DanushkaDissanayaka/Qbot/arduino-Src/lineFollow.h

#ifndef lineFollow_h
    #define lineFollow_h
    #include "QTRSensor.h"
    #include "motor.h"
    #include "irSensor.h"

    #define LINE_FLLOW_DEBUG    false

    // Full speed PID Values
    double FULL_SPEED_Kp =  0.158;//0.080; 0.340
    double FULL_SPEED_Kd =  20;//0.890; 1.71
    #define FULL_SPEED_Ki   0

    #define BACKWORD_STOP_DELAY     80 // no need
    #define ROTATE_STOP_DELAY       40

    // Half Speed PID values
    #define HALF_SPEED_Kp 0
    #define HALF_SPEED_Kd 0
    #define HALF_SPEED_Ki 0

    #define LINE_POSITION   3500
    #define MIN_VALUE       200
    #define MAX_VALUE       600

    //turning speed values
    #define TURN_SPEED      120
    #define TUNING_SPEED    100

    int             error       = 0;
    int             I           = 0;
    int             lastError   = 0;
    int             motorSpeed  = 0;
    unsigned int    position    = 0;
    bool junctionDetect = false;

    void calPid (float Kp , float Kd , float Ki){
        position = qtra.readLine(sensorValues);
        error =  position - LINE_POSITION;
        I = I + error;
        motorSpeed = (Kp * error) + (Kd * (error - lastError)) + I*Ki;
        lastError = error;
    }

    void fullSpeedLineFollowBlackStrip(void){
        forward(); // make both motors rotate forward
        clear_ISR_Verialble(); // before start line follow clear ISR variables
        while(1){

            calPid(FULL_SPEED_Kp,FULL_SPEED_Kd,FULL_SPEED_Ki); // calculate pid For left and right motors

            if(sensorValues[0] < MIN_VALUE &&sensorValues[1] < MIN_VALUE && sensorValues[2] < MIN_VALUE && sensorValues[3] < MIN_VALUE && sensorValues[4] < MIN_VALUE && sensorValues[5] < MIN_VALUE && sensorValues[6] < MIN_VALUE && sensorValues[7] < MIN_VALUE){
                // lost our line or this canbe dedend
                //backToLine();
                break;
            }
            /*if(sensorValues[0] > MAX_VALUE &&sensorValues[1] > MAX_VALUE && sensorValues[2] > MAX_VALUE && sensorValues[3] > MAX_VALUE && sensorValues[4] > MAX_VALUE && sensorValues[5] > MAX_VALUE && sensorValues[6] > MAX_VALUE && sensorValues[7] > MAX_VALUE){
                break; // found our solution
            }*/
            if (leftDetect || rightDetect){
                junctionDetect = true;
                break; // found a junction
            }
            rightMotorSpeed = FULL_BASE_SPEED_RIGHT - motorSpeed;
            leftMotorSpeed =  FULL_BASE_SPEED_LEFT  + motorSpeed;

            if (rightMotorSpeed > FULL_MOTOR_SPEED_RIGHT )  rightMotorSpeed = FULL_MOTOR_SPEED_RIGHT; // prevent the motor from going beyond max speed
            if (leftMotorSpeed >  FULL_MOTOR_SPEED_LEFT )   leftMotorSpeed  = FULL_MOTOR_SPEED_LEFT; // prevent the motor from going beyond max speed
            if (rightMotorSpeed < 0) rightMotorSpeed = 0; // keep the motor speed positive
            if (leftMotorSpeed < 0) leftMotorSpeed = 0; // keep the motor speed positive   

            if (LINE_FLLOW_DEBUG) {
                Serial.print(position);
                Serial.print("\t");
                Serial.print(error);
                Serial.print("\t");
                Serial.print(leftMotorSpeed);
                Serial.print("\t");
                Serial.print(rightMotorSpeed);
                Serial.print("\t");
                Serial.println();
            }
            else {
                speedControl(leftMotorSpeed,rightMotorSpeed); // change motor speed according PID values
            }
        }
        //ForwordBreak();
    }

    void fullSpeedLineFollowWhiteStrip(void){
        
        while(1){

            calPid(FULL_SPEED_Kp,FULL_SPEED_Kd,FULL_SPEED_Ki); // calculate pid For left and right motors

            if(sensorValues[0] < MIN_VALUE && sensorValues[1] < MIN_VALUE && sensorValues[2] < MIN_VALUE && sensorValues[3] < MIN_VALUE && sensorValues[4] < MIN_VALUE && sensorValues[5] < MIN_VALUE && sensorValues[6] < MIN_VALUE && sensorValues[7] < MIN_VALUE){
                    break; // found our solution
            }

            if(sensorValues[0] > MAX_VALUE && sensorValues[1] > MAX_VALUE && sensorValues[2] > MAX_VALUE && sensorValues[3] > MAX_VALUE && sensorValues[4] > MAX_VALUE && sensorValues[5] > MAX_VALUE && sensorValues[6] > MAX_VALUE && sensorValues[7] > MAX_VALUE){
                // lost our line or this canbe dedend
                //backToLine();
                break;
            }

            rightMotorSpeed = FULL_BASE_SPEED_RIGHT + motorSpeed;
            leftMotorSpeed =  FULL_BASE_SPEED_LEFT  - motorSpeed;

            if (rightMotorSpeed > FULL_MOTOR_SPEED_RIGHT )  rightMotorSpeed = FULL_MOTOR_SPEED_RIGHT; // prevent the motor from going beyond max speed
            if (leftMotorSpeed >  FULL_MOTOR_SPEED_LEFT )   leftMotorSpeed  = FULL_MOTOR_SPEED_LEFT; // prevent the motor from going beyond max speed
            if (rightMotorSpeed < 0) rightMotorSpeed = 0; // keep the motor speed positive
            if (leftMotorSpeed < 0) leftMotorSpeed = 0; // keep the motor speed positive   

            if (LINE_FLLOW_DEBUG) {
                Serial.print(position);
                Serial.print("\t");
                Serial.print(error);
                Serial.print("\t");
                Serial.print(leftMotorSpeed);
                Serial.print("\t");
                Serial.print(rightMotorSpeed);
                Serial.print("\t");
                Serial.println();
            }
            else {
                forward();
                speedControl(leftMotorSpeed,rightMotorSpeed); // change motor speed according PID values
            }
        }
        Stop(); // stop both motors after line Follow
    }

    void backToLine(void){
        speedControl(120,120);
        backward();
        delay(50);
        Stop();
    }

    void BlackTuneLine(void){
        // tune line after turn
    }

    void BlackLinetTurnLeft(void){
        //turn right with line referance
        speedControl(0,0);
        turnRight();

        position = qtra.readLine(sensorValues);

         while(sensorValues[6] < MIN_VALUE){
             position = qtra.readLine(sensorValues);
             speedControl(TURN_SPEED,TURN_SPEED);
         }

            speedControl(0,0);
            turnRight();
            position = qtra.readLine(sensorValues);

            while(sensorValues[6] > MAX_VALUE && sensorValues[3] < MIN_VALUE){
             position = qtra.readLine(sensorValues);
             speedControl(TUNING_SPEED,TUNING_SPEED);
            }
        turnLeft();
        delay(ROTATE_STOP_DELAY);
        Stop();
    }

    void BlackLineTurnRight(void){
            // turn left with line referance
        speedControl(0,0);
        turnLeft();

        position = qtra.readLine(sensorValues);

         while(sensorValues[1] < MIN_VALUE){
             position = qtra.readLine(sensorValues);
             speedControl(TURN_SPEED,TURN_SPEED);
         }

        speedControl(0,0);
        turnLeft();
        position = qtra.readLine(sensorValues);

            while(sensorValues[1] > MAX_VALUE && sensorValues[4] < MIN_VALUE){
             position = qtra.readLine(sensorValues);
             speedControl(TUNING_SPEED,TUNING_SPEED);
            }
        turnRight();
        delay(ROTATE_STOP_DELAY);
        Stop();
    }
#endif
